longestcow/roboticHand/fingerModels/fingerIndexRing/stl/middle.stl

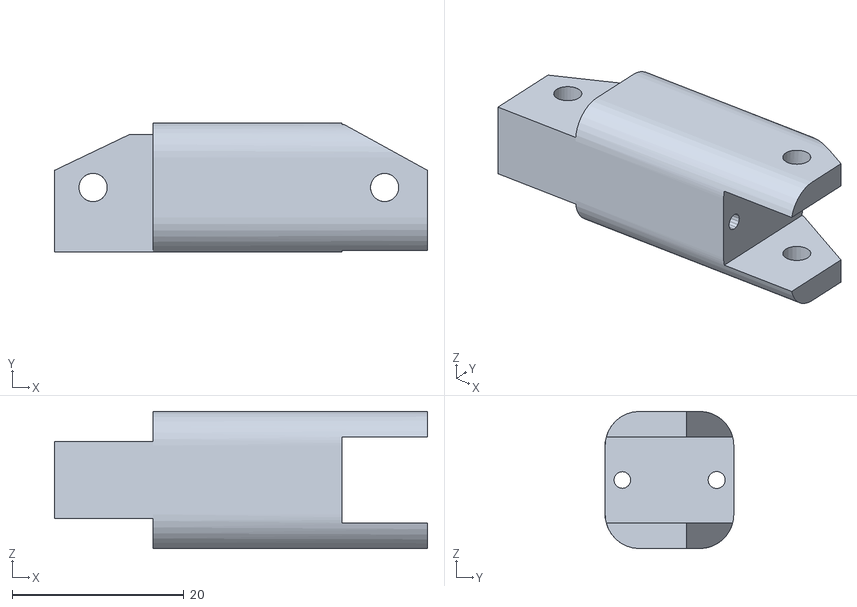
[picture p15: CAD file, 2024-06-10]
fingerModels/fingerIndexRing/stl/middle.stl
43.5 x 15.0 x 16.0
