longestcow/roboticHand/fingerModels/fingerPinky/stl/top.stl

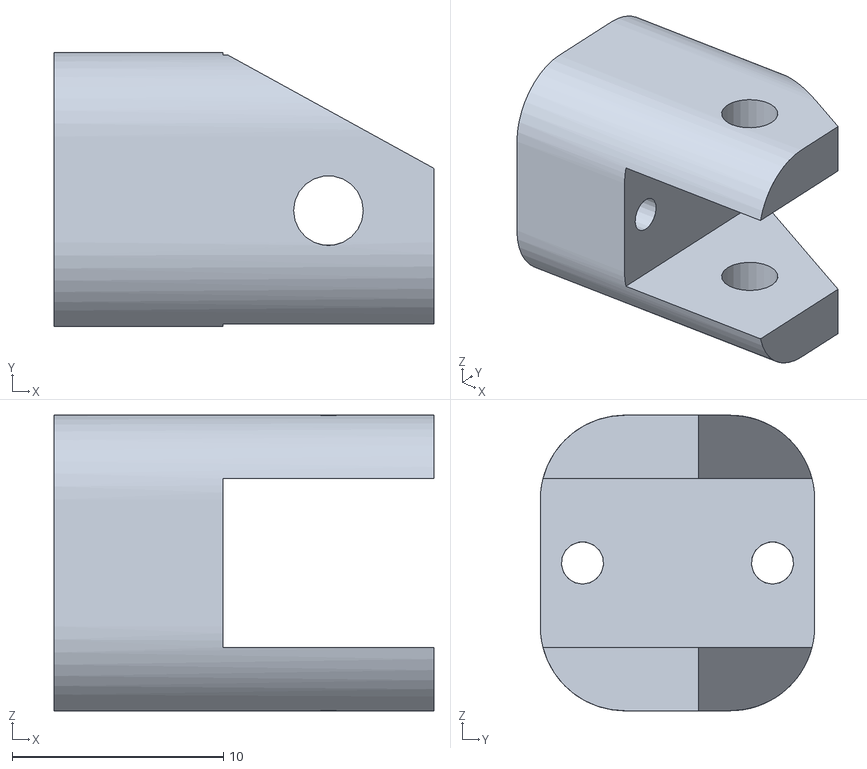
[picture p16: CAD file, 2024-06-10]
fingerModels/fingerPinky/stl/top.stl
18.0 x 13.0 x 14.0
