longestcow/roboticHand/fingerModels/fingerThumb/stls/middleThumb.stl

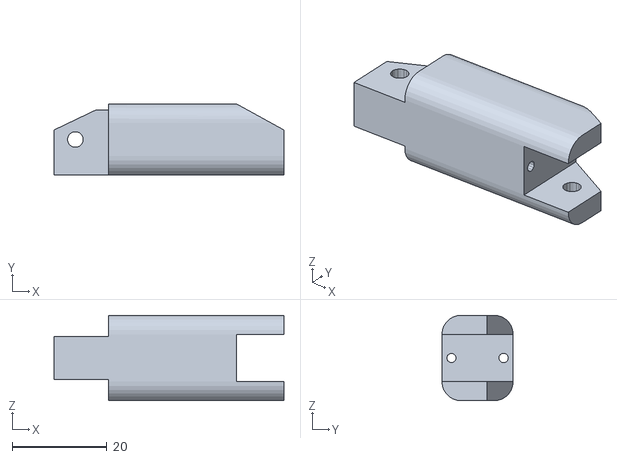
[picture p17: CAD file, 2024-06-19]
fingerModels/fingerThumb/stls/middleThumb.stl
48.5 x 15.0 x 18.0
