longestcow/roboticHand/fingerModels/fingerMiddle/stl/top.stl

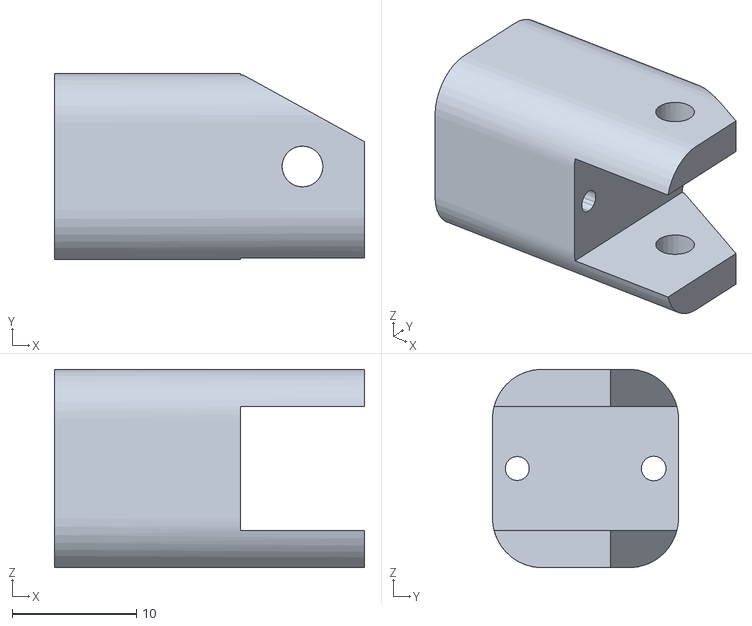
[picture p18: CAD file, 2024-06-10]
fingerModels/fingerMiddle/stl/top.stl
25.0 x 15.0 x 16.0
